ZPilot/kakave/Community/photo/2.0_bot.jpg

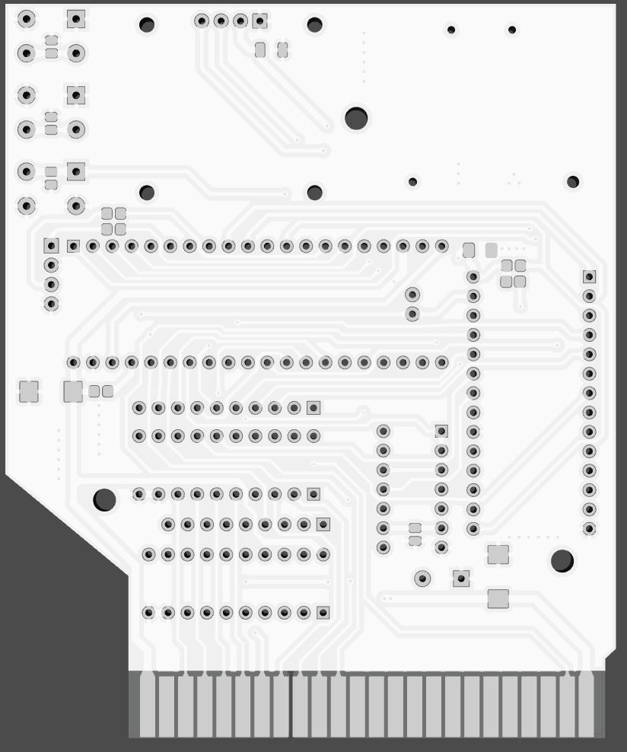
Community/photo/2.0_bot.jpg
