ZPilot/kakave/photo/make1.jpg

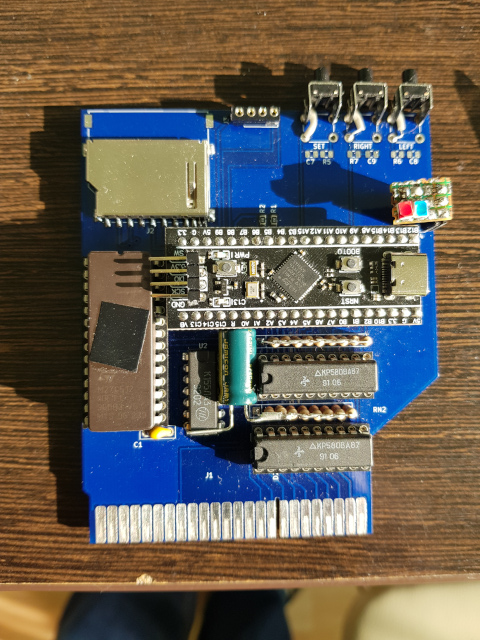
photo/make1.jpg
