ZPilot/kakave/photo/make.jpg

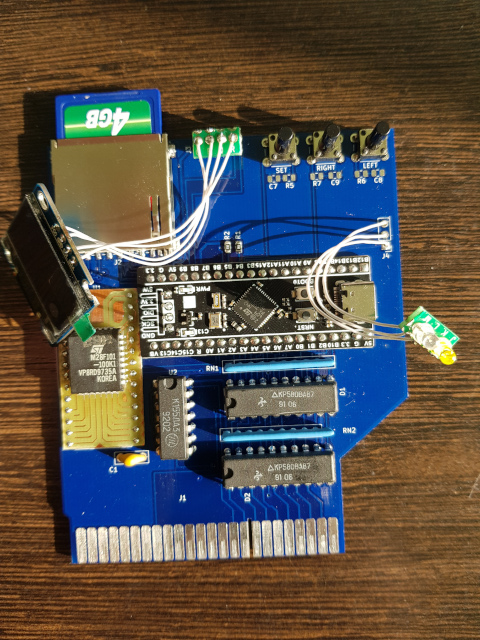
photo/make.jpg
