ZPilot/kakave/firmware401/Core/Src/ctrl128/rawtrack.c

/*
 * rawtrack.c
 *
 *  Created on: 6 июн. 2020 г.
 *      Author: alex
 */
#include "ctrl128.h"

const uint16_t rawtrk00[SECTORLEN/2]={
	0x4E4E, 0x4E4E, 0x4E4E, 0x4E4E, 0x4E4E, 0x4E4E, 0x4E4E, 0x4E4E,
	0x4E4E, 0x4E4E, 0x4E4E, 0x4E4E, 0x4E4E, 0x4E4E, 0x4E4E, 0x4E4E,
	0x4E4E, 0x4E4E, 0x0000, 0x0000, 0x0000, 0x0000, 0x0000, 0x0000,
	0xA1A1, 0xFEA1, 0x0000, 0x0201, 0x1593, 0x4E4E, 0x4E4E, 0x4E4E,
	0x4E4E, 0x4E4E, 0x4E4E, 0x4E4E, 0x4E4E, 0x4E4E, 0x4E4E, 0x4E4E,
	0x4E4E, 0x0000, 0x0000, 0x0000, 0x0000, 0x0000, 0x0000, 0xA1A1,
	0xFBA1, 0x4040, 0x4040, 0x4040, 0x4040, 0x4040, 0x4040, 0x4040,
	0x4040, 0x4040, 0x4040, 0x4040, 0x4040, 0x4040, 0x4040, 0x4040,
	0x4040, 0x4040, 0x4040, 0x4040, 0x4040, 0x4040, 0x4040, 0x4040,
	0x4040, 0x4040, 0x4040, 0x4040, 0x4040, 0x4040, 0x4040, 0x4040,
	0x4040, 0x4040, 0x4040, 0x4040, 0x4040, 0x4040, 0x4040, 0x4040,
	0x4040, 0x4040, 0x4040, 0x4040, 0x4040, 0x4040, 0x4040, 0x4040,
	0x4040, 0x4040, 0x4040, 0x4040, 0x4040, 0x4040, 0x4040, 0x4040,
	0x4040, 0x4040, 0x4040, 0x4040, 0x4040, 0x4040, 0x4040, 0x4040,
	0x4040, 0x4040, 0x4040, 0x4040, 0x4040, 0x4040, 0x4040, 0x4040,
	0x4040, 0x4040, 0x4040, 0x4040, 0x4040, 0x4040, 0x4040, 0x4040,
	0x4040, 0x4040, 0x4040, 0x4040, 0x4040, 0x4040, 0x4040, 0x4040,
	0x4040, 0x4040, 0x4040, 0x4040, 0x4040, 0x4040, 0x4040, 0x4040,
	0x4040, 0x4040, 0x4040, 0x4040, 0x4040, 0x4040, 0x4040, 0x4040,
	0x4040, 0x4040, 0x4040, 0x4040, 0x4040, 0x4040, 0x4040, 0x4040,
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
	0x5080, 0x5080, 0x5080, 0x5080, 0x5080, 0x5080, 0x5080, 0x5080,
	0x5080, 0x5080, 0x5080, 0x5080, 0x5080, 0x5080, 0x5080, 0x5080,
	0x5080, 0x5080, 0x5080, 0x5080, 0x5080, 0x5080, 0x5080, 0x5080,
	0x5080, 0x5080, 0x5080, 0x5080, 0x5080, 0x5080, 0x5080, 0x5080,
	0x5080, 0x6080, 0x0080
};
