ZPilot/kakave/firmware401/Core/Src/ctrl128/testtrk1.c

/*
 * testtrk1.c
 *
 *  Created on: 31 июл. 2020 г.
 *      Author: alex
 */

#include "ctrl128.h"

const uint8_t testtrk[FLOPPY_DATATRACKSIZE*2]={
	0xA0, 0x00, 0x05, 0x00, 0x04, 0x01, 0x00, 0x00, 0x00, 0x00, 0x10, 0x43, 0x10, 0x9C, 0x00, 0x01,
	0x37, 0x08, 0x24, 0x00, 0x0D, 0x00, 0x00, 0x00, 0x00, 0x0A, 0x3F, 0x42, 0x4F, 0x4F, 0x54, 0x2D,
	0x55, 0x2D, 0x4E, 0x6F, 0x20, 0x62, 0x6F, 0x6F, 0x74, 0x20, 0x6F, 0x6E, 0x20, 0x76, 0x6F, 0x6C,
	0x75, 0x6D, 0x65, 0x0D, 0x0A, 0x0A, 0x80, 0x00, 0xDF, 0x8B, 0x74, 0xFF, 0xFD, 0x80, 0x1F, 0x94,
	0x76, 0xFF, 0xFA, 0x80, 0xFF, 0x01, 0x00, 0x00, 0x00, 0x00, 0x00, 0x00, 0x00, 0x00, 0x00, 0x00,
	0x00, 0x00, 0x00, 0x00, 0x00, 0x00, 0x00, 0x00, 0x00, 0x00, 0x00, 0x00, 0x00, 0x00, 0x00, 0x00,
	0x00, 0x00, 0x00, 0x00, 0x00, 0x00, 0x00, 0x00, 0x00, 0x00, 0x00, 0x00, 0x00, 0x00, 0x00, 0x00,
	0x00, 0x00, 0x00, 0x00, 0x00, 0x00, 0x00, 0x00, 0x00, 0x00, 0x00, 0x00, 0x00, 0x00, 0x00, 0x00,
	0x00, 0x00, 0x00, 0x00, 0x00, 0x00, 0x00, 0x00, 0x00, 0x00, 0x00, 0x00, 0x00, 0x00, 0x00, 0x00,
	0x00, 0x00, 0x00, 0x00, 0x00, 0x00, 0x00, 0x00, 0x00, 0x00, 0x00, 0x00, 0x00, 0x00, 0x00, 0x00,
	0x00, 0x00, 0x00, 0x00, 0x00, 0x00, 0x00, 0x00, 0x00, 0x00, 0x00, 0x00, 0x00, 0x00, 0x00, 0x00,
	0x00, 0x00, 0x00, 0x00, 0x00, 0x00, 0x00, 0x00, 0x00, 0x00, 0x00, 0x00, 0x00, 0x00, 0x00, 0x00,
	0x00, 0x00, 0x00, 0x00, 0x00, 0x00, 0x00, 0x00, 0x00, 0x00, 0x00, 0x00, 0x00, 0x00, 0x00, 0x00,
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
	0x00, 0x00, 0x00, 0x00, 0x00, 0x00, 0x00, 0x00, 0x00, 0x00, 0x00, 0x00, 0x00, 0x00, 0x00, 0x00,
	0x00, 0x00, 0x00, 0x00, 0x00, 0x00, 0x00, 0x00, 0x00, 0x00, 0x00, 0x00, 0x00, 0x00, 0x00, 0x00,
	0x00, 0x00, 0x00, 0x00, 0x00, 0x00, 0x00, 0x00, 0x00, 0x00, 0x00, 0x00, 0x00, 0x00, 0x00, 0x00,
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
};
